sb-ocr/3d-printed-nas/Enclosure/CAD/3MF/Structure/Base.3mf

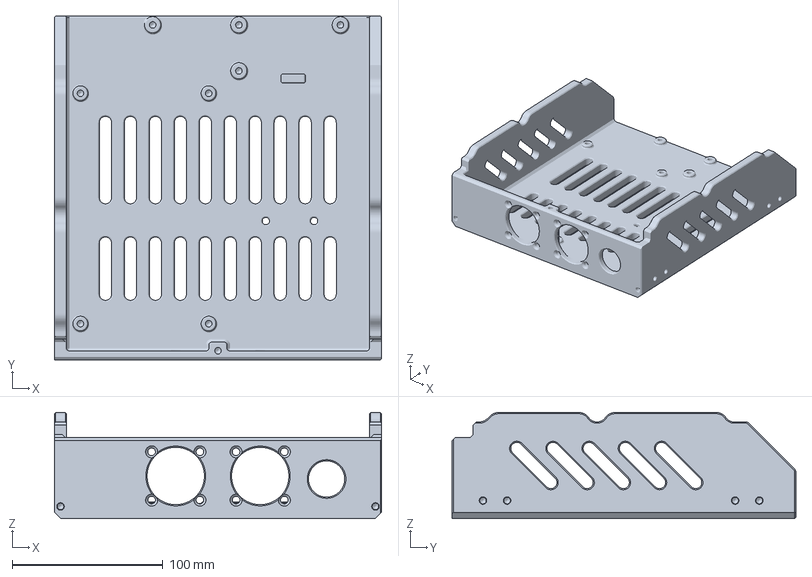
[picture p16: CAD file, 2025-05-03]
Enclosure/CAD/3MF/Structure/Base.3mf
216.8 x 227.8 x 70.3 mm
