sb-ocr/3d-printed-nas/Enclosure/CAD/3MF/Structure/PCIe card support.3mf

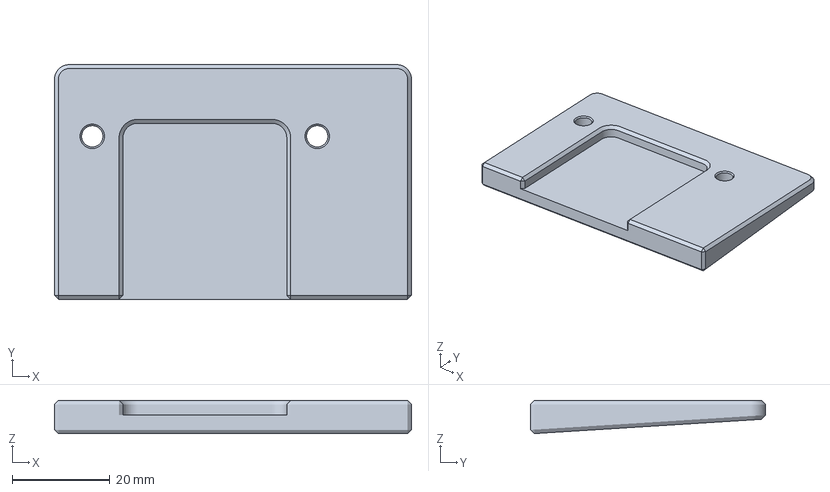
[picture p17: CAD file, 2025-05-03]
Enclosure/CAD/3MF/Structure/PCIe card support.3mf
73.0 x 48.0 x 6.78 mm
