sb-ocr/3d-printed-nas/Enclosure/CAD/3MF/Structure/Front grill.3mf

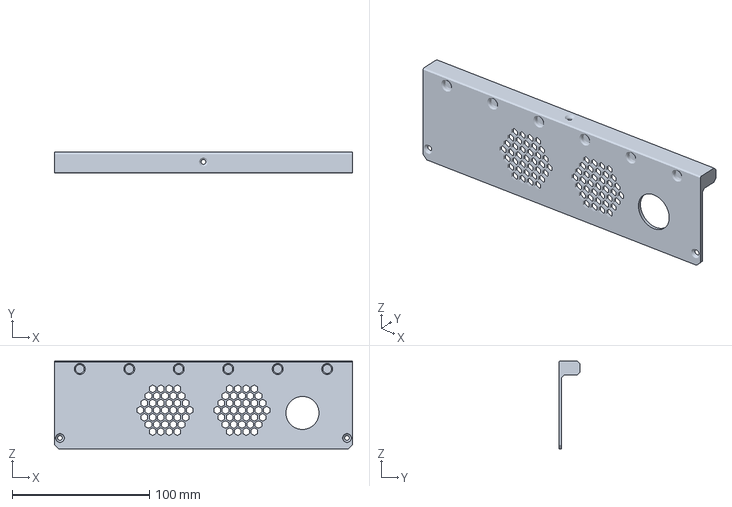
[picture p18: CAD file, 2025-05-03]
Enclosure/CAD/3MF/Structure/Front grill.3mf
216.8 x 15.6 x 64.0 mm
